Zekonze/Capstone-Project/gaskalibrasi.ino

#include <MQ2_LPG.h>

// 1. Add the 4 missing hardware constants required by the library
#define RL_Value   2022.0   // Typical load resistor value used in this library
#define Ro_Value   5.46     // Clean air base resistance calibration factor
#define Volt_Value 5.0      // VCC supply voltage for the sensor 
#define ADC_Value  4095.0   // ESP32 uses a 12-bit ADC (0 to 4095)

// 2. Keep your original mathematical curve definitions
#define x1_Value 199.150007852152
#define x2_Value 797.3322752256328
#define y1_Value 1.664988323698715
#define y2_Value 0.8990240080541785
#define x_Value 497.4177875376839
#define y_Value 1.0876679972710004

#define MQ2_PIN 0 // Replace with your actual ESP32 analog pin
MQ2Sensor mq2(MQ2_PIN);

void setup() {
  Serial.begin(115200);
  mq2.begin();
  
  // FIXED: Pass all 10 arguments in the precise sequence the library expects
  mq2.setCalibration(
    RL_Value, Ro_Value, Volt_Value, ADC_Value, 
    x_Value, x1_Value, x2_Value, y_Value, y1_Value, y2_Value
  );
}

void loop() {
  // Read current gas level in PPM
  float ppm = mq2.readGas(); 

  Serial.print("LPG Level: ");
  Serial.print(ppm);
  Serial.println(" PPM");

  // Keep your threshold logic here to sense danger only at 3000++ PPM
  if (ppm >= 3000.0) {
    Serial.println("⚠️ DANGER! Gas level exceeds 3000 PPM! ⚠️");
    // Trigger alarm pin, buzzer, or relay here
  } else {
    Serial.println("Status: Safe");
  }

  delay(1000); 
}
